makersmakingchange/Project-Core-3D-Symbols/Photos/Project-Core-3D-Symbol-Good.jpg

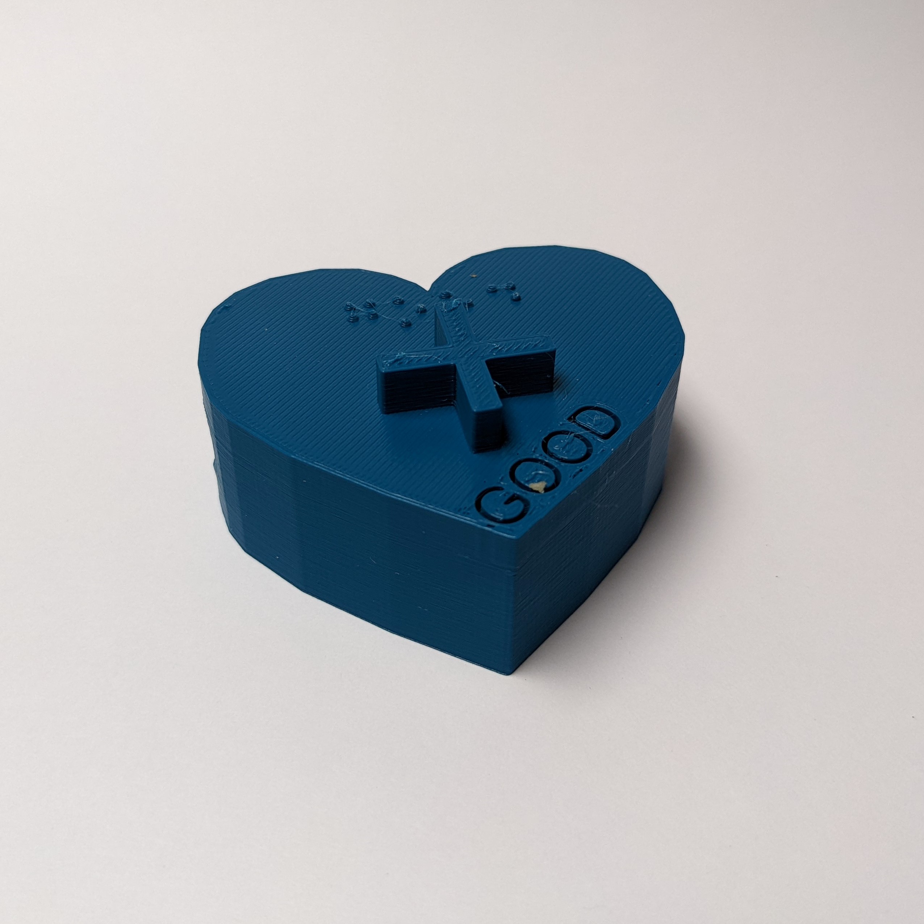
Photos/Project-Core-3D-Symbol-Good.jpg
