makersmakingchange/Project-Core-3D-Symbols/Photos/Project-Core-3D-Symbol-Not.jpg

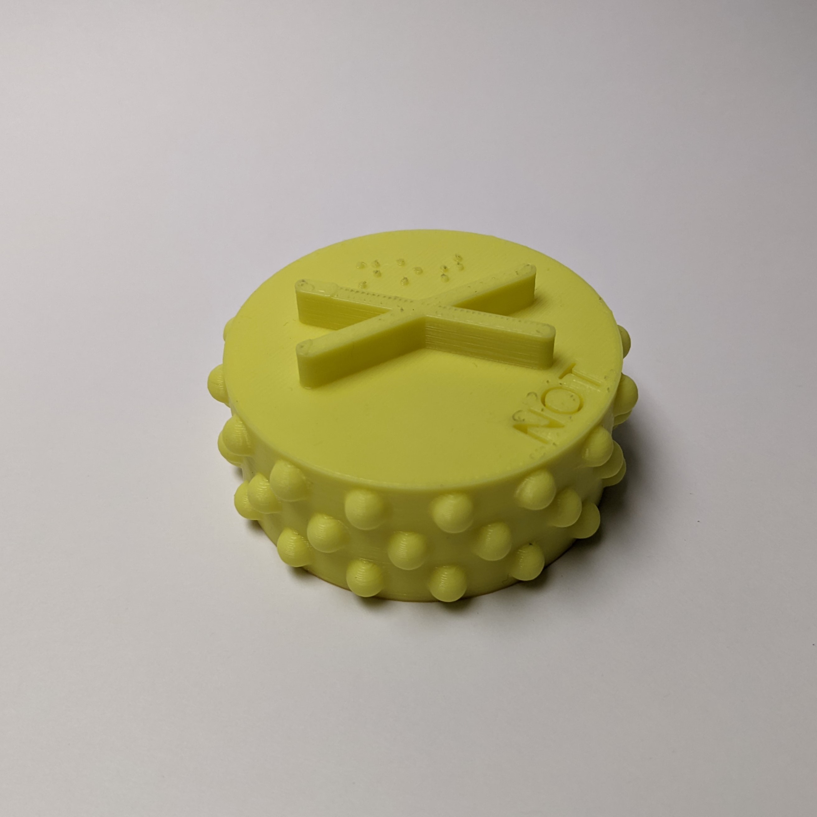
Photos/Project-Core-3D-Symbol-Not.jpg
